7m4gmh/7seg-panel/hardware/056-sparse/7seg-panel-056-display-wide/production/bom.csv

Designator | Footprint | Quantity | Value | LCSC Part #
J100, J101, J102 | PinHeader_2x04_P2.54mm_Vertical | 3 | Conn_02x04_Odd_Even
U100, U101, U102, U103, U104, U105, U106, U107, U108, U109, U110, U111, U112, U113, U114, U115 | 7SegmentLED_OSL10564 | 16 | OSL10564-IRA
