7m4gmh/7seg-panel/hardware/056/7seg-led/production/bom.csv

Designator | Footprint | Quantity | Value | LCSC Part #
J201, J202, J203 | PinHeader_2x04_P2.54mm_Vertical | 3 | Conn_02x04_Odd_Even
U201, U202, U203, U204, U205, U206, U207, U208 | SL-9263 | 8 | DA56-11EWA
