7m4gmh/7seg-panel/hardware/040/7seg-panel-control-040-single/7seg-panel-control-040-single.kicad_pcb

## KiCad design hardware/040/7seg-panel-control-040-single/7seg-panel-control-040-single.kicad_pcb (2026-03-19)

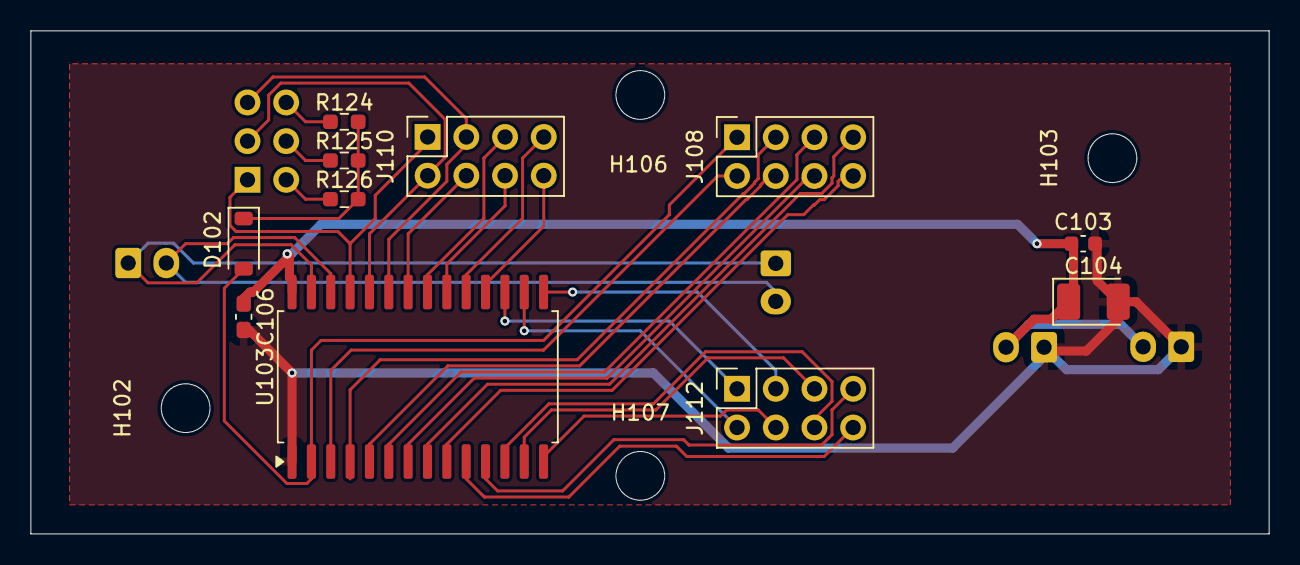
[picture p28: board 7seg-panel-control-040-single.kicad_pcb from above]

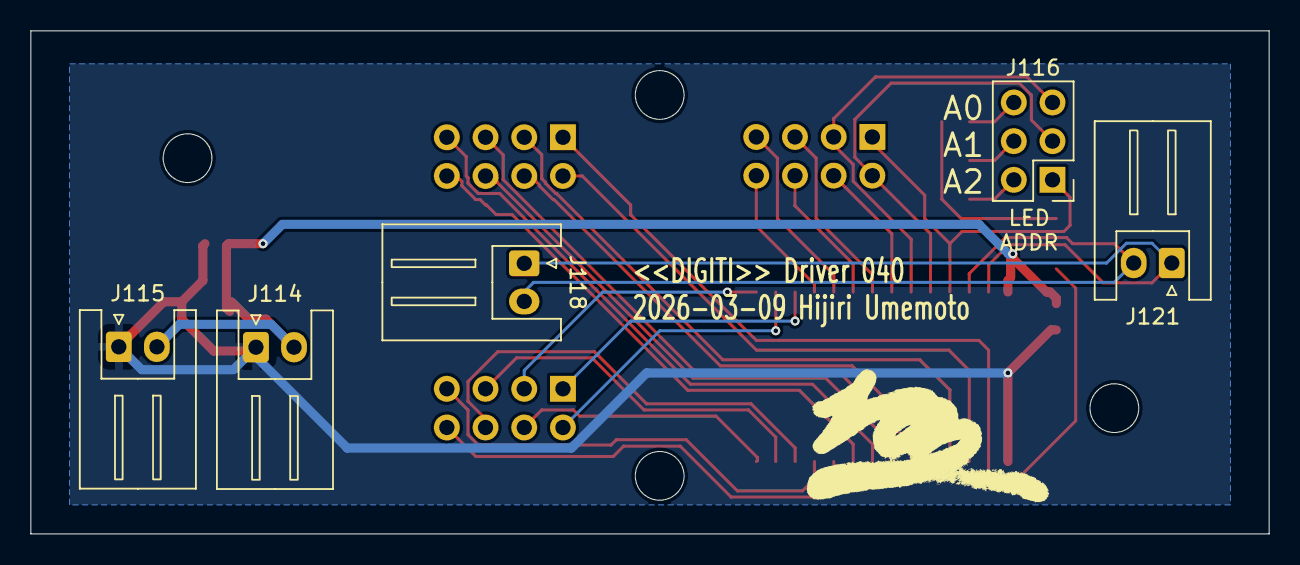
[picture p29: board 7seg-panel-control-040-single.kicad_pcb from below]

Board: 2 copper layers, 81.3 x 33.0 mm, 20 parts (5 on the bottom side), 32 nets.

Parts:
C103: 22uF; C_0603_1608Metric
C104: 22uF; CP_EIA-3528-21_Kemet-B_HandSolder
C106: 0.1uF; C_0603_1608Metric_Pad1.08x0.95mm_HandSolder
D102: 1N4148W; D_SOD-123
H102, H103, H106, H107: MountingHole; MountingHole_3.2mm_M3
J108, J110, J112: Conn_02x04_Odd_Even; PinSocket_2x04_P2.54mm_Vertical
J114, J115: +5V; JST_XH_S2B-XH-A_1x02_P2.50mm_Horizontal
J116: Conn_02x03_Odd_Even; PinHeader_2x03_P2.54mm_Vertical
J118, J121: I2C; JST_XH_S2B-XH-A_1x02_P2.50mm_Horizontal
R124, R125, R126: 39kR; R_0603_1608Metric_Pad0.98x0.95mm_HandSolder
U103: HT16K33-28-SOPA; SOP-28_8.4x18.16mm_P1.27mm

Connections:
COM0: D102.2 (A), J108.1, U103.2 (COM0/AD)
COM1: J108.2, U103.3 (COM1/KS0)
COM2: J108.3, U103.4 (COM2/KS1)
COM3: J108.4, U103.5 (COM3/KS2)
COM4: J108.5, U103.6 (COM4)
COM5: J108.6, U103.7 (COM5)
COM6: J108.7, U103.8 (COM6)
COM7: J108.8, U103.9 (COM7)
GND: C103.2, C104.2, C106.2, J114.1, J115.1, U103.1 (VSS)
unnamed: D102.1 (K), R124.1, R125.1, R126.1
unnamed: J116.2, R126.2
unnamed: J116.4, R125.2
unnamed: J116.6, R124.2
ROW0: J110.1, J116.1, U103.25 (ROW0/A2)
ROW1: J110.2, J116.3, U103.24 (ROW1/A1)
ROW2: J110.3, J116.5, U103.23 (ROW2/A0)
ROW3: J110.4, U103.22 (ROW3/K1)
ROW4: J110.5, U103.21 (ROW4/K2)
ROW5: J110.6, U103.20 (ROW5/K3)
ROW6: J110.7, U103.19 (ROW6/K4)
ROW7: J110.8, U103.18 (ROW7/K5)
ROW8: J112.1, U103.17 (ROW8/K6)
ROW9: J112.2, U103.16 (ROW9/K7)
ROW10: J112.3, U103.15 (ROW10/K8)
ROW11: J112.4, U103.14 (ROW11/K9)
ROW12: J112.5, U103.13 (ROW12/K10)
ROW13: J112.6, U103.12 (ROW13/K12)
ROW14: J112.7, U103.11 (ROW14/K12)
ROW15: J112.8, U103.10 (ROW15/K13/INT)
SCL: J118.2, J121.2, U103.26 (SCL)
SDA: J118.1, J121.1, U103.27 (SDA)
VDD: C103.1, C104.1, C106.1, J114.2, J115.2, U103.28 (VDD)
