7m4gmh/7seg-panel/hardware/056/7seg-led/7seg-led.kicad_pcb

## KiCad design hardware/056/7seg-led/7seg-led.kicad_pcb (2025-10-05)

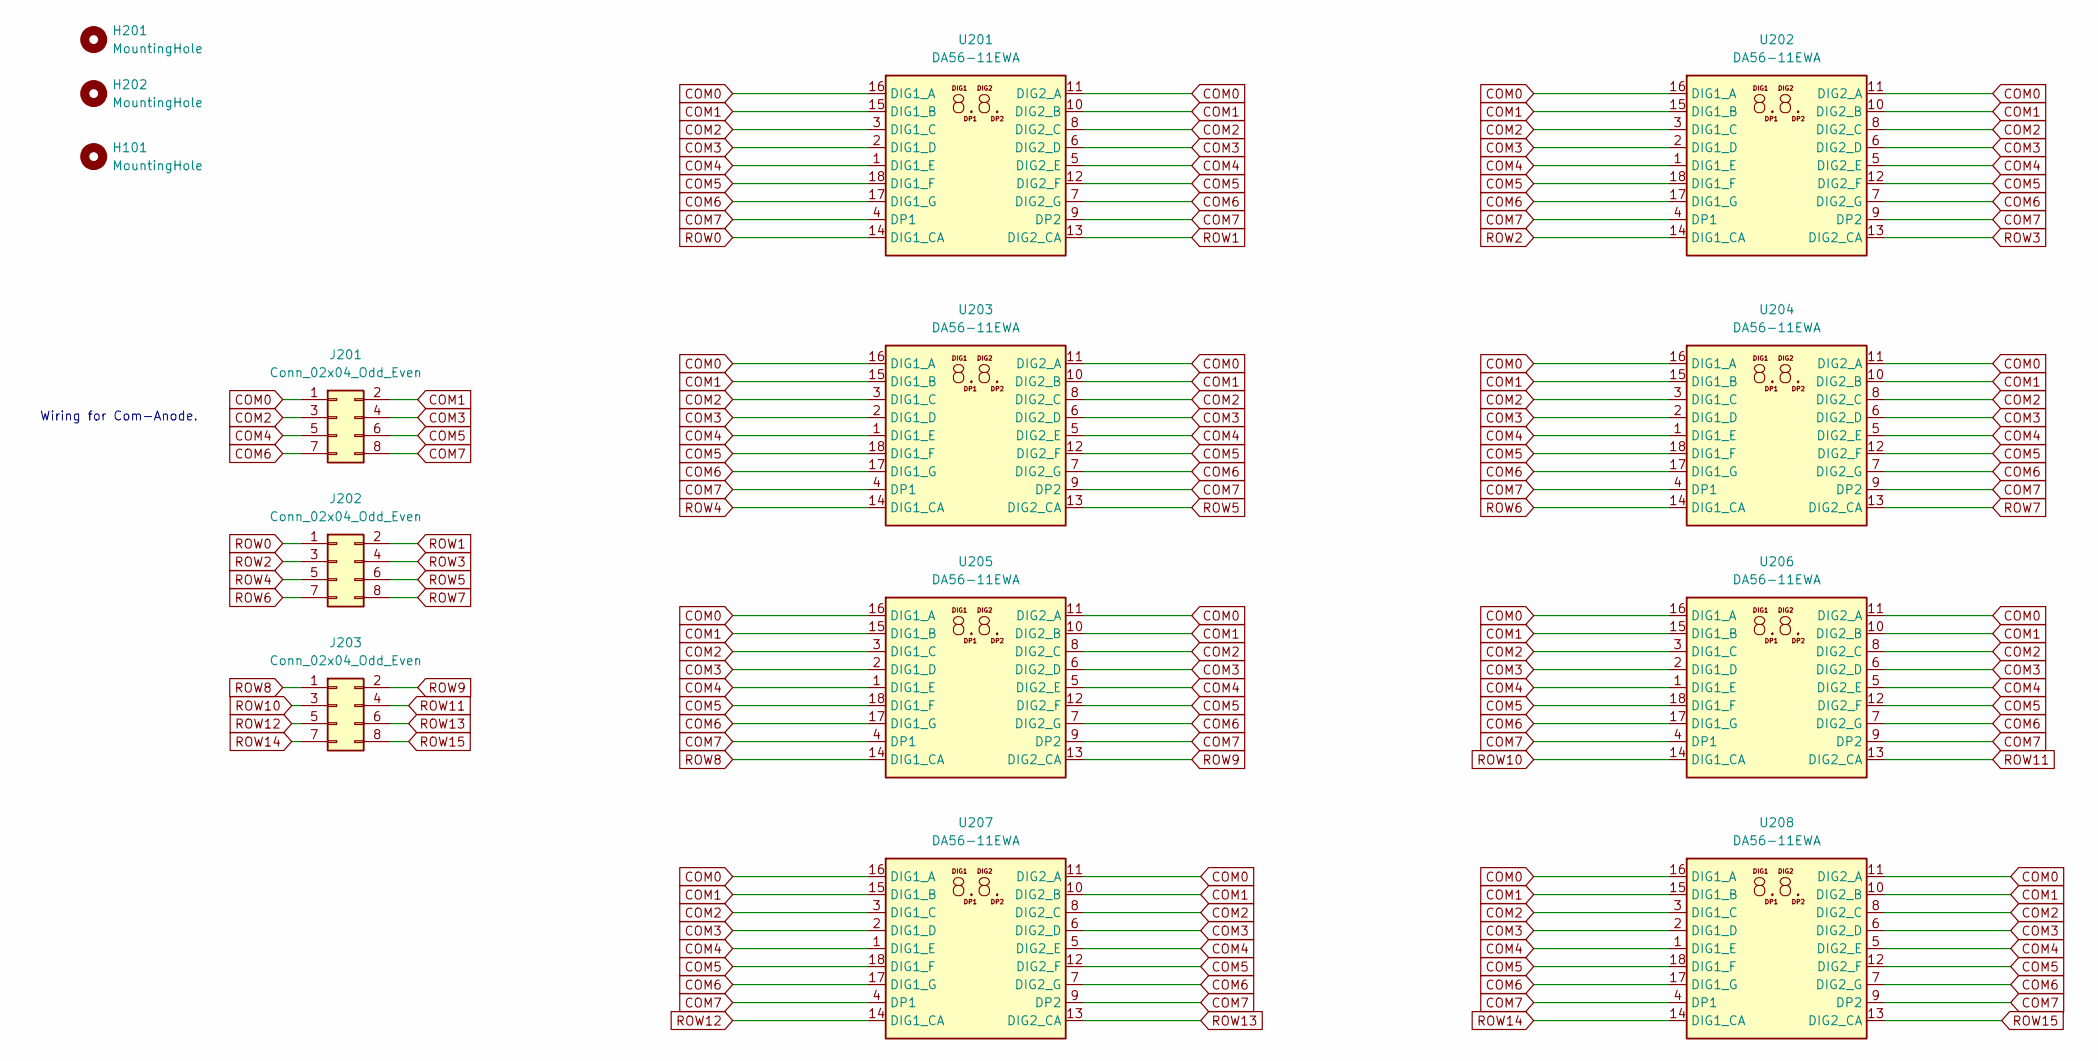
[picture p30: schematic 7seg-led.kicad_sch, 7-seg LED panel]

Parts:
H101, H201, H202: MountingHole; MountingHole_3.2mm_M3
J201, J202, J203: Conn_02x04_Odd_Even; PinHeader_2x04_P2.54mm_Vertical
U201, U202, U203, U204, U205, U206, U207, U208: DA56-11EWA; SL-9263

Connections:
COM0: J201.1, U201.11 (DIG2_A), U201.16 (DIG1_A), U202.11 (DIG2_A), U202.16 (DIG1_A), U203.11 (DIG2_A), U203.16 (DIG1_A), U204.11 (DIG2_A), U204.16 (DIG1_A), U205.11 (DIG2_A), U205.16 (DIG1_A), U206.11 (DIG2_A), U206.16 (DIG1_A), U207.11 (DIG2_A), U207.16 (DIG1_A), U208.11 (DIG2_A), U208.16 (DIG1_A)
COM1: J201.2, U201.10 (DIG2_B), U201.15 (DIG1_B), U202.10 (DIG2_B), U202.15 (DIG1_B), U203.10 (DIG2_B), U203.15 (DIG1_B), U204.10 (DIG2_B), U204.15 (DIG1_B), U205.10 (DIG2_B), U205.15 (DIG1_B), U206.10 (DIG2_B), U206.15 (DIG1_B), U207.10 (DIG2_B), U207.15 (DIG1_B), U208.10 (DIG2_B), U208.15 (DIG1_B)
COM2: J201.3, U201.3 (DIG1_C), U201.8 (DIG2_C), U202.3 (DIG1_C), U202.8 (DIG2_C), U203.3 (DIG1_C), U203.8 (DIG2_C), U204.3 (DIG1_C), U204.8 (DIG2_C), U205.3 (DIG1_C), U205.8 (DIG2_C), U206.3 (DIG1_C), U206.8 (DIG2_C), U207.3 (DIG1_C), U207.8 (DIG2_C), U208.3 (DIG1_C), U208.8 (DIG2_C)
COM3: J201.4, U201.2 (DIG1_D), U201.6 (DIG2_D), U202.2 (DIG1_D), U202.6 (DIG2_D), U203.2 (DIG1_D), U203.6 (DIG2_D), U204.2 (DIG1_D), U204.6 (DIG2_D), U205.2 (DIG1_D), U205.6 (DIG2_D), U206.2 (DIG1_D), U206.6 (DIG2_D), U207.2 (DIG1_D), U207.6 (DIG2_D), U208.2 (DIG1_D), U208.6 (DIG2_D)
COM4: J201.5, U201.1 (DIG1_E), U201.5 (DIG2_E), U202.1 (DIG1_E), U202.5 (DIG2_E), U203.1 (DIG1_E), U203.5 (DIG2_E), U204.1 (DIG1_E), U204.5 (DIG2_E), U205.1 (DIG1_E), U205.5 (DIG2_E), U206.1 (DIG1_E), U206.5 (DIG2_E), U207.1 (DIG1_E), U207.5 (DIG2_E), U208.1 (DIG1_E), U208.5 (DIG2_E)
COM5: J201.6, U201.12 (DIG2_F), U201.18 (DIG1_F), U202.12 (DIG2_F), U202.18 (DIG1_F), U203.12 (DIG2_F), U203.18 (DIG1_F), U204.12 (DIG2_F), U204.18 (DIG1_F), U205.12 (DIG2_F), U205.18 (DIG1_F), U206.12 (DIG2_F), U206.18 (DIG1_F), U207.12 (DIG2_F), U207.18 (DIG1_F), U208.12 (DIG2_F), U208.18 (DIG1_F)
COM6: J201.7, U201.7 (DIG2_G), U201.17 (DIG1_G), U202.7 (DIG2_G), U202.17 (DIG1_G), U203.7 (DIG2_G), U203.17 (DIG1_G), U204.7 (DIG2_G), U204.17 (DIG1_G), U205.7 (DIG2_G), U205.17 (DIG1_G), U206.7 (DIG2_G), U206.17 (DIG1_G), U207.7 (DIG2_G), U207.17 (DIG1_G), U208.7 (DIG2_G), U208.17 (DIG1_G)
COM7: J201.8, U201.4 (DP1), U201.9 (DP2), U202.4 (DP1), U202.9 (DP2), U203.4 (DP1), U203.9 (DP2), U204.4 (DP1), U204.9 (DP2), U205.4 (DP1), U205.9 (DP2), U206.4 (DP1), U206.9 (DP2), U207.4 (DP1), U207.9 (DP2), U208.4 (DP1), U208.9 (DP2)
ROW0: J202.1, U201.14 (DIG1_CA)
ROW1: J202.2, U201.13 (DIG2_CA)
ROW2: J202.3, U202.14 (DIG1_CA)
ROW3: J202.4, U202.13 (DIG2_CA)
ROW4: J202.5, U203.14 (DIG1_CA)
ROW5: J202.6, U203.13 (DIG2_CA)
ROW6: J202.7, U204.14 (DIG1_CA)
ROW7: J202.8, U204.13 (DIG2_CA)
ROW8: J203.1, U205.14 (DIG1_CA)
ROW9: J203.2, U205.13 (DIG2_CA)
ROW10: J203.3, U206.14 (DIG1_CA)
ROW11: J203.4, U206.13 (DIG2_CA)
ROW12: J203.5, U207.14 (DIG1_CA)
ROW13: J203.6, U207.13 (DIG2_CA)
ROW14: J203.7, U208.14 (DIG1_CA)
ROW15: J203.8, U208.13 (DIG2_CA)

Notes on the sheet:
Wiring for Com-Anode.

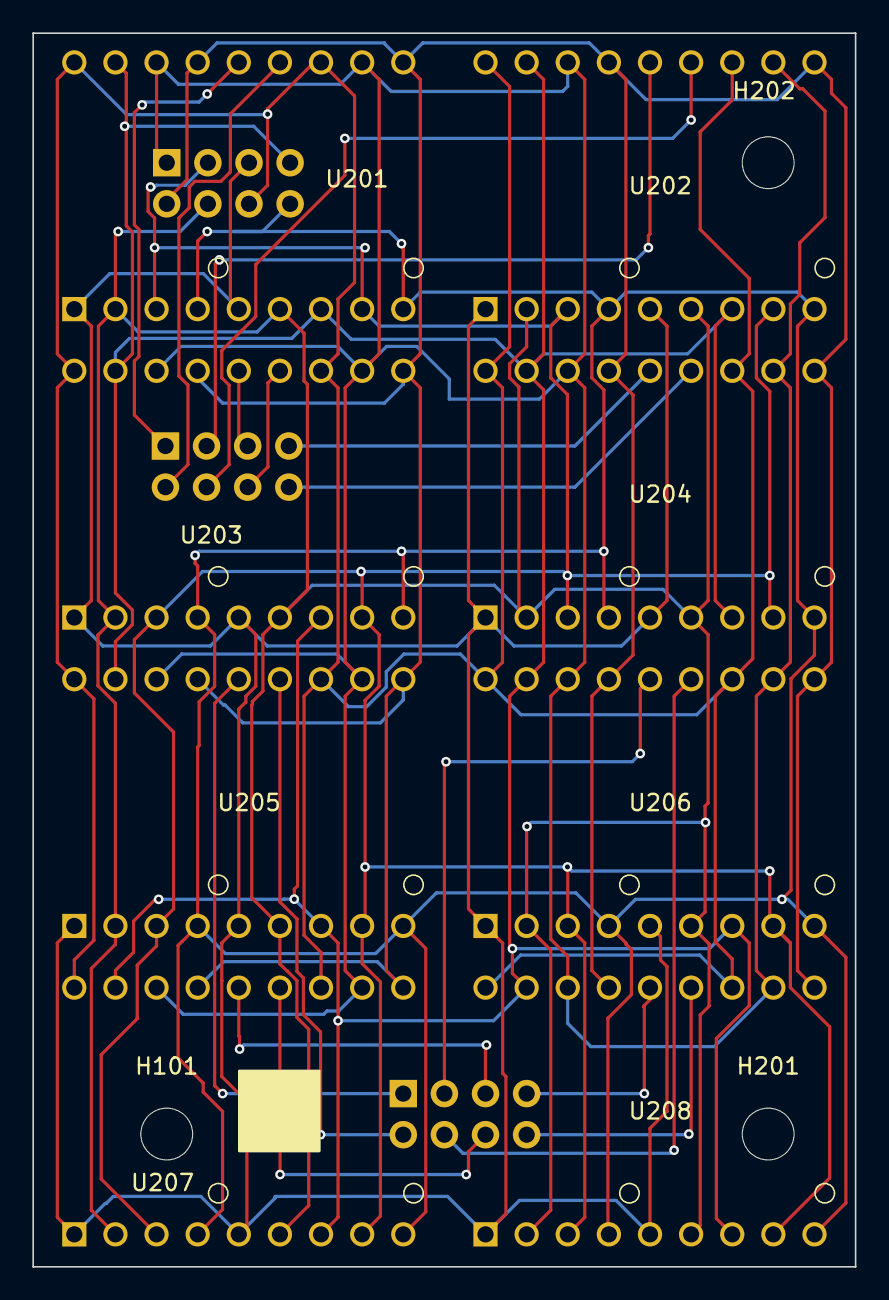
[picture p31: board 7seg-led.kicad_pcb from above]

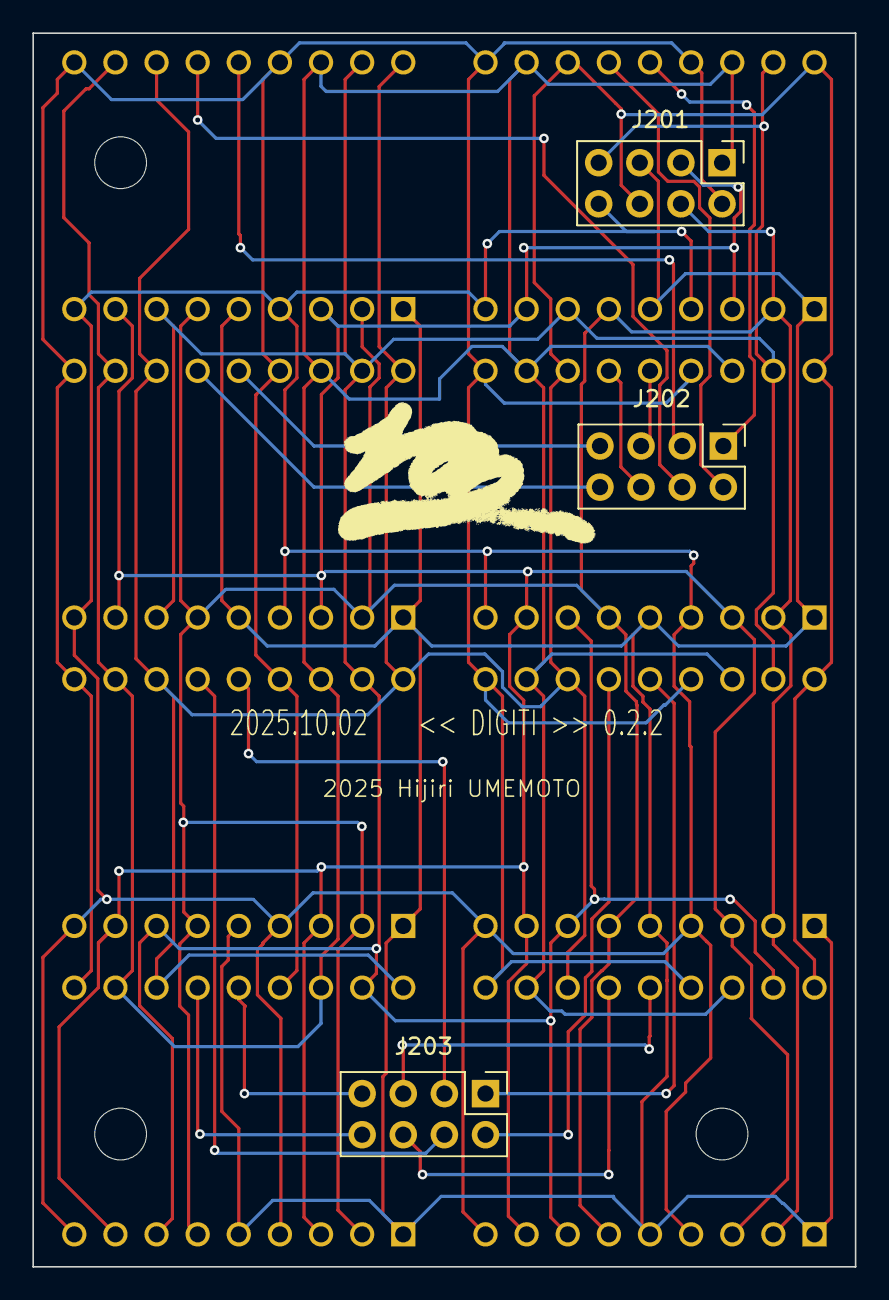
[picture p32: board 7seg-led.kicad_pcb from below]

Board: 2 copper layers, 50.8 x 76.2 mm, 14 parts (3 on the bottom side), 24 nets.
