7m4gmh/7seg-panel/hardware/7seg-hat/7seg-hat.kicad_pcb

## KiCad design hardware/7seg-hat/7seg-hat.kicad_pcb (2025-09-08)

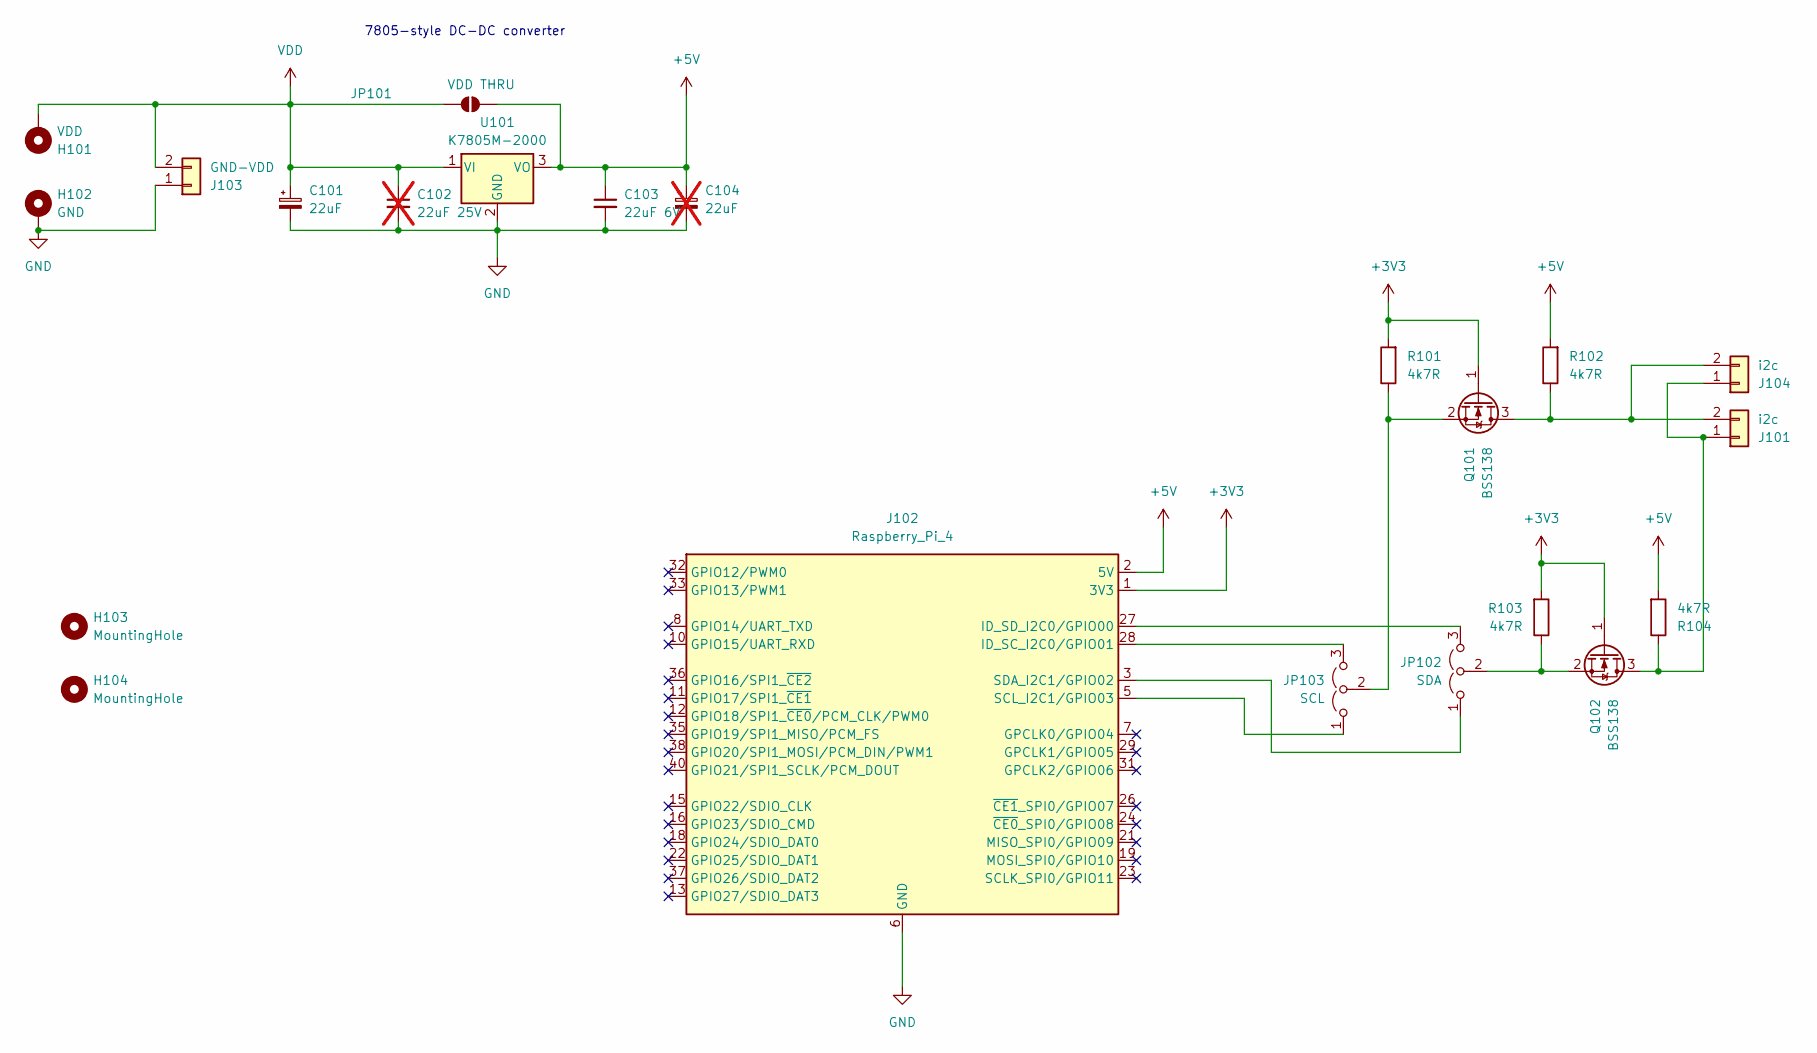
[picture p33: schematic 7seg-hat.kicad_sch]

Parts:
C101: 22uF; CP_EIA-3528-21_Kemet-B
C102: 22uF 25V; C_0603_1608Metric_Pad1.08x0.95mm_HandSolder; not fitted
C103: 22uF 6V; C_0603_1608Metric_Pad1.08x0.95mm_HandSolder
C104: 22uF; CP_EIA-3528-21_Kemet-B; not fitted
H101: VDD; MountingHole_3.2mm_M3_DIN965_Pad
H102: GND; MountingHole_3.2mm_M3_DIN965_Pad
H103, H104: MountingHole; MountingHole_3.2mm_M3
J101, J104: i2c; JST_XH_S2B-XH-A-1_1x02_P2.50mm_Horizontal
J102: Raspberry_Pi_4; RPI_Hat_B+
J103: GND-VDD; JST_XH_S2B-XH-A-1_1x02_P2.50mm_Horizontal
JP101: VDD THRU; SolderJumper-2_P1.3mm_Open_TrianglePad1.0x1.5mm
JP102: SDA; PinHeader_1x03_P2.54mm_Vertical
JP103: SCL; PinHeader_1x03_P2.54mm_Vertical
Q101, Q102: BSS138; SOT-23_Handsoldering
R101, R102, R103, R104: 4k7R; R_0603_1608Metric_Pad0.98x0.95mm_HandSolder
U101: K7805M-2000; TO-220-3_Vertical

Connections:
+3V3: J102.1 (3V3), J102.17 (3V3), Q101.1 (G), Q102.1 (G), R101.2, R103.2
+5V: C103.1, C104.1, J102.2 (5V), J102.4 (5V), JP101.2 (B), R102.2, R104.2, U101.3 (VO)
GND: C101.2, C102.2, C103.2, C104.2, H102.1 (MP), J102.6 (GND), J102.9 (GND), J102.14 (GND), J102.20 (GND), J102.25 (GND), J102.30 (GND), J102.34 (GND), J102.39 (GND), J103.1, U101.2 (GND)
unnamed: J101.1, J104.1, Q102.3 (D), R104.1
unnamed: J101.2, J104.2, Q101.3 (D), R102.1
unnamed: J102.28 (ID_SC_I2C0/GPIO01), JP103.3 (B)
unnamed: J102.27 (ID_SD_I2C0/GPIO00), JP102.3 (B)
unnamed: J102.5 (SCL_I2C1/GPIO03), JP103.1 (A)
unnamed: J102.3 (SDA_I2C1/GPIO02), JP102.1 (A)
unnamed: JP102.2 (C), Q102.2 (S), R103.1
unnamed: JP103.2 (C), Q101.2 (S), R101.1
VDD: C101.1, C102.1, H101.1 (MP), J103.2, JP101.1 (A), U101.1 (VI)

Notes on the sheet:
7805-style DC-DC converter

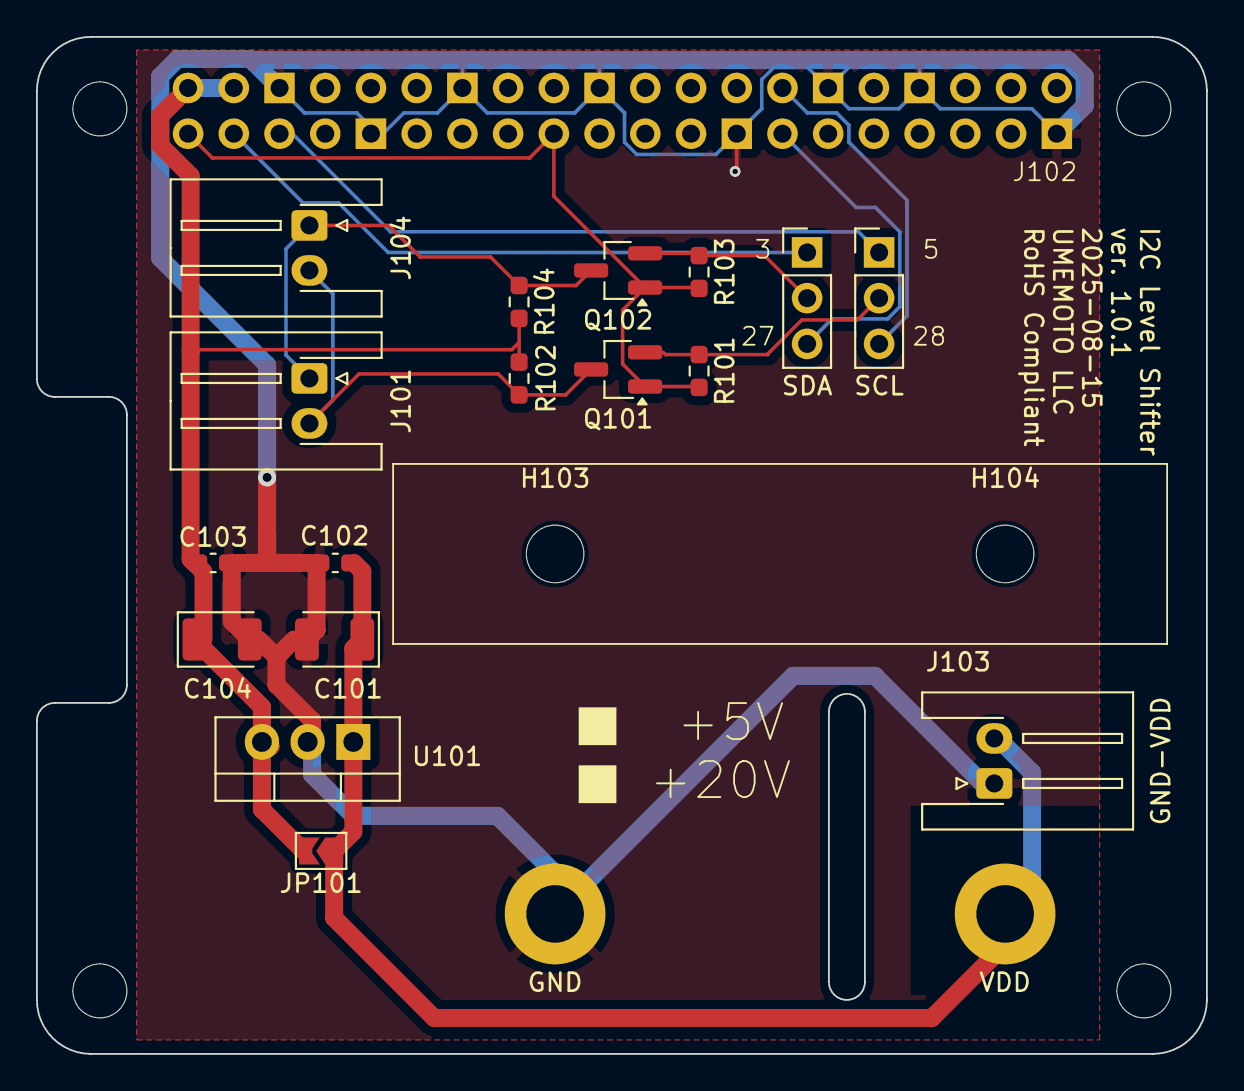
[picture p34: board 7seg-hat.kicad_pcb from above]

Board: 2 copper layers, 65.0 x 56.5 mm, 22 parts (0 on the bottom side), 12 nets.
