7m4gmh/7seg-panel/include/config.h

// src/config.h
#pragma once

#include <vector>
#include <string>
#include <numeric>
#include <map>
#include <algorithm> // for std::sort, std::unique

extern double CHAR_WIDTH_MM;
extern double CHAR_HEIGHT_MM;

// TCA9548A の構成を定義する構造体
struct TCA9548AConfig {
    int address; // TCA9548A のアドレス (-1 で直接接続)
    std::map<int, std::vector<std::vector<int>>> channels; // channel -> slave address grid
    std::map<int, std::tuple<int, int, int>> rows; // row -> (channel, row_offset, col_offset)
};

// Bus の構成を定義する構造体
struct BusConfig {
    std::vector<TCA9548AConfig> tca9548as;
};

// パネルの物理構成を定義する構造体
struct DisplayConfig {
    std::string name;
    std::string type; // "physical" or "emulator"
    std::map<int, BusConfig> buses;
    int module_digits_width;
    int module_digits_height;
    int total_width;
    int total_height;

    // Optional: per-module digit size override by module I2C address
    // key: module address (int), value: pair(width, height)
    std::map<int, std::pair<int,int>> module_sizes_by_address;
    // Optional: per-module column-order reversal flag by module I2C address
    // key: module address (int), value: true if module columns should be reversed
    std::map<int,bool> module_column_reverse;
    // Optional: per-module explicit index mapping (linear index mapping)
    // key: module address (int), value: array of length (module_width*module_height)
    // mapping[logical_index] = physical_index
    std::map<int,std::vector<int>> module_index_map;

    int total_digits() const { return total_width * total_height; }

    // Get module digit width/height for a specific module address.
    // If no override exists, return the global module_digits_width/height.
    std::pair<int,int> module_size_for_address(int addr) const {
        auto it = module_sizes_by_address.find(addr);
        if (it != module_sizes_by_address.end()) return it->second;
        return { module_digits_width, module_digits_height };
    }

    bool module_columns_reversed(int addr) const {
        auto it = module_column_reverse.find(addr);
        if (it != module_column_reverse.end()) return it->second;
        return false;
    }

    const std::vector<int>* module_index_map_for_address(int addr) const {
        auto it = module_index_map.find(addr);
        if (it != module_index_map.end()) return &it->second;
        return nullptr;
    }

    std::vector<int> all_addresses() const {
        std::vector<int> addrs;
        for (const auto& [bus_id, bus_config] : buses) {
            for (const auto& tca : bus_config.tca9548as) {
                for (const auto& [channel, grid] : tca.channels) {
                    for (const auto& row : grid) {
                        addrs.insert(addrs.end(), row.begin(), row.end());
                    }
                }
            }
        }
        std::sort(addrs.begin(), addrs.end());
        addrs.erase(std::unique(addrs.begin(), addrs.end()), addrs.end());
        return addrs;
    }
};


// LEDキャラクター1つの物理的な寸法 (mm)
extern double CHAR_WIDTH_MM;
extern double CHAR_HEIGHT_MM;
