7m4gmh/7seg-panel/include/common.h

// src/common.h
#pragma once

#include "config.h"

#include <atomic>
#include <deque>
#include <mutex>
#include <vector>

#ifndef COMMON_H
#define COMMON_H

#include <cstdint>
#include <csignal>

// Ctrl+C / SIGTERM で立つ終了フラグ
extern std::atomic<bool> g_should_exit;

// シグナルハンドラ設定用
void setup_signal_handlers();


// I2Cバスをconfig.jsonから選択する
int open_i2c_auto(const DisplayConfig& config);
bool initialize_displays(int i2c_fd, const DisplayConfig& config);

#endif

// --- アプリケーション設定値  ---
constexpr int PORT = 9999;
const int W = 640;
const int H = 480;
constexpr int FPS = 15;
constexpr int AUDIO_CHUNK_SIZE = 2048;
constexpr int FRAMES_PER_BUFFER = 1024;
constexpr int SAMPLE_RATE = 48000;
constexpr int CHANNELS = 2; // 1 for monoral, 2 for stereo

// --- グローバル変数 ---
extern std::atomic<bool> finished;
extern std::atomic<bool> audio_waiting;
extern std::mutex audio_mtx;
extern std::deque<std::vector<char>> audio_buf;

extern std::mutex frame_mtx;
extern std::vector<uint8_t> latest_frame;
extern std::atomic<int> last_pts_ms;
extern double start_time;
extern int audio_bytes_received;


/**
 * @brief I2Cバスの通信エラーからの復旧を試みる関数
 * 
 * @param i2c_fd 参照渡しのI2Cファイルディスクリプタ。復旧成功時に新しい値で更新される。
 * @param config ディスプレイ設定。再初期化に必要。
 * @return true 復旧に成功した場合
 * @return false 復旧に失敗した場合
 */
bool attempt_i2c_recovery(int& i2c_fd, const DisplayConfig& config);

// 利用可能な I2C デバイスを自動検出してオープン (/dev/i2c-0 → /dev/i2c-1 の順)
// 成功時はファイルディスクリプタ、失敗時は -1 を返す
int open_i2c_auto();

struct I2CErrorInfo {
    int channel = -1; // エラーが発生したTCAのチャンネル番号
    int address = -1; // エラーが発生したI2Cデバイスのアドレス
    bool error_occurred = false; // エラーが発生したかどうか
};
